Allyson-Robert/SpaceTimeGlobe/Images/001-A.png

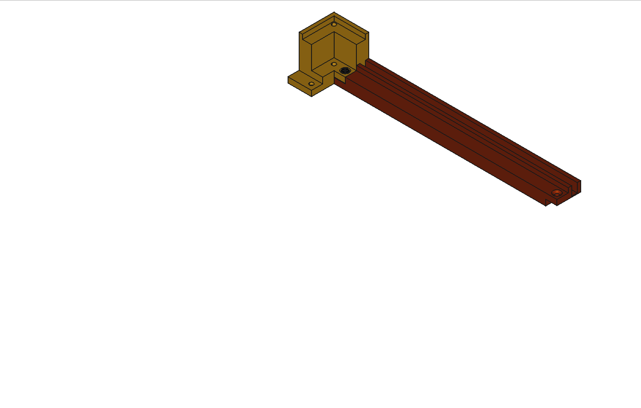
Images/001-A.png
