Allyson-Robert/SpaceTimeGlobe/Images/001.png

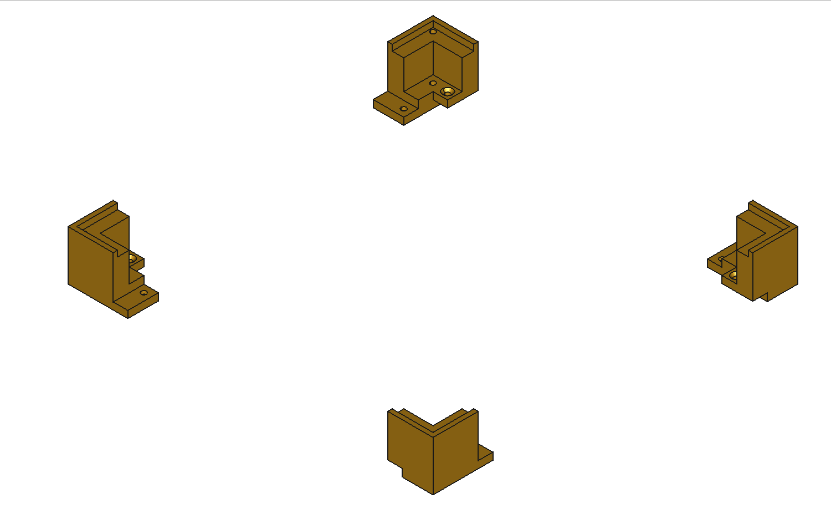
Images/001.png
