Allyson-Robert/SpaceTimeGlobe/Images/002.png

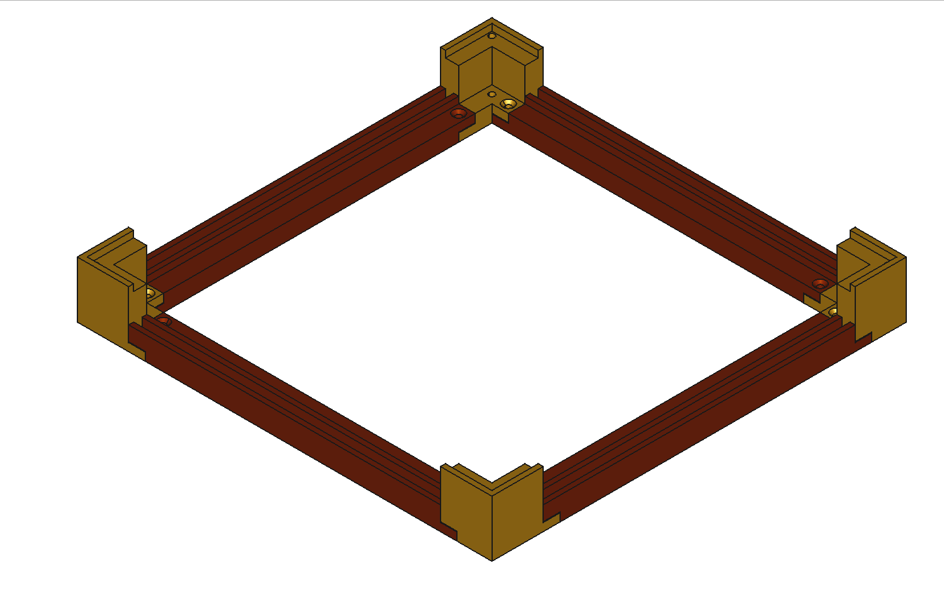
Images/002.png
