Allyson-Robert/SpaceTimeGlobe/Images/004.png

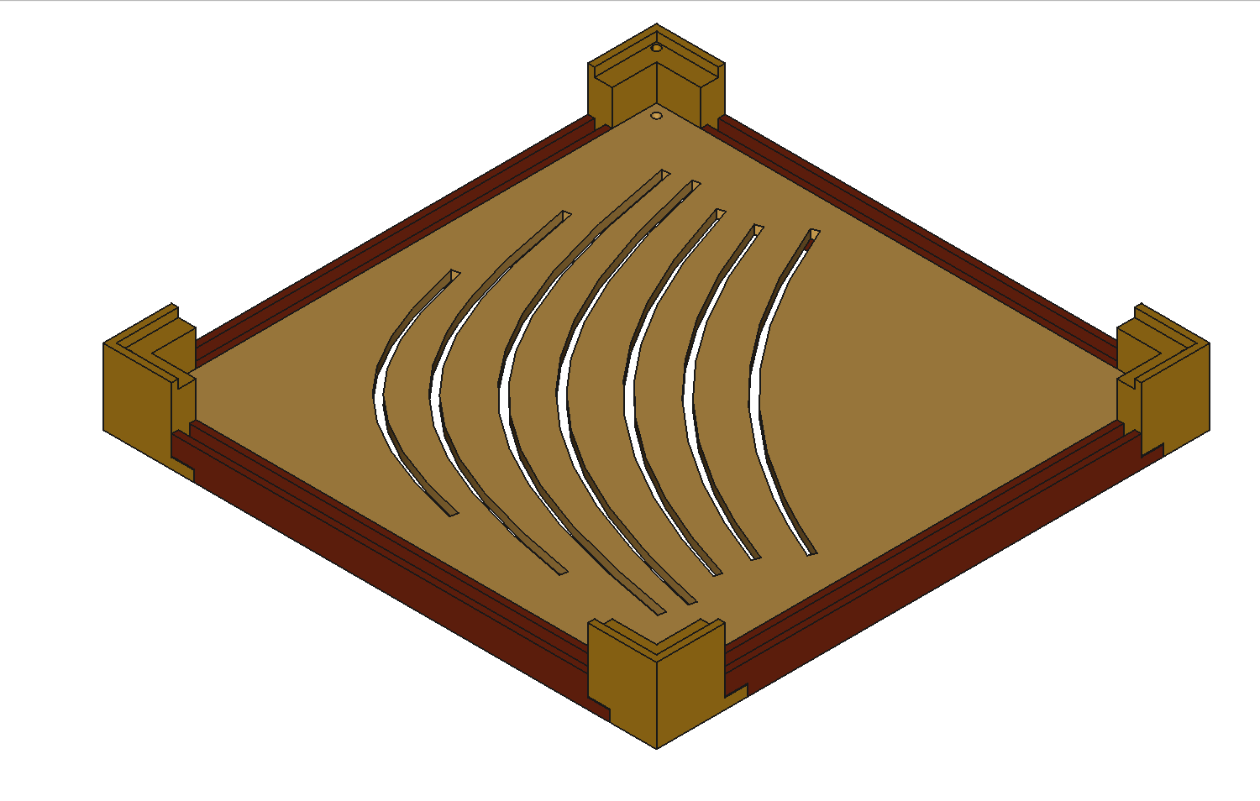
Images/004.png
