Allyson-Robert/SpaceTimeGlobe/Images/007.png

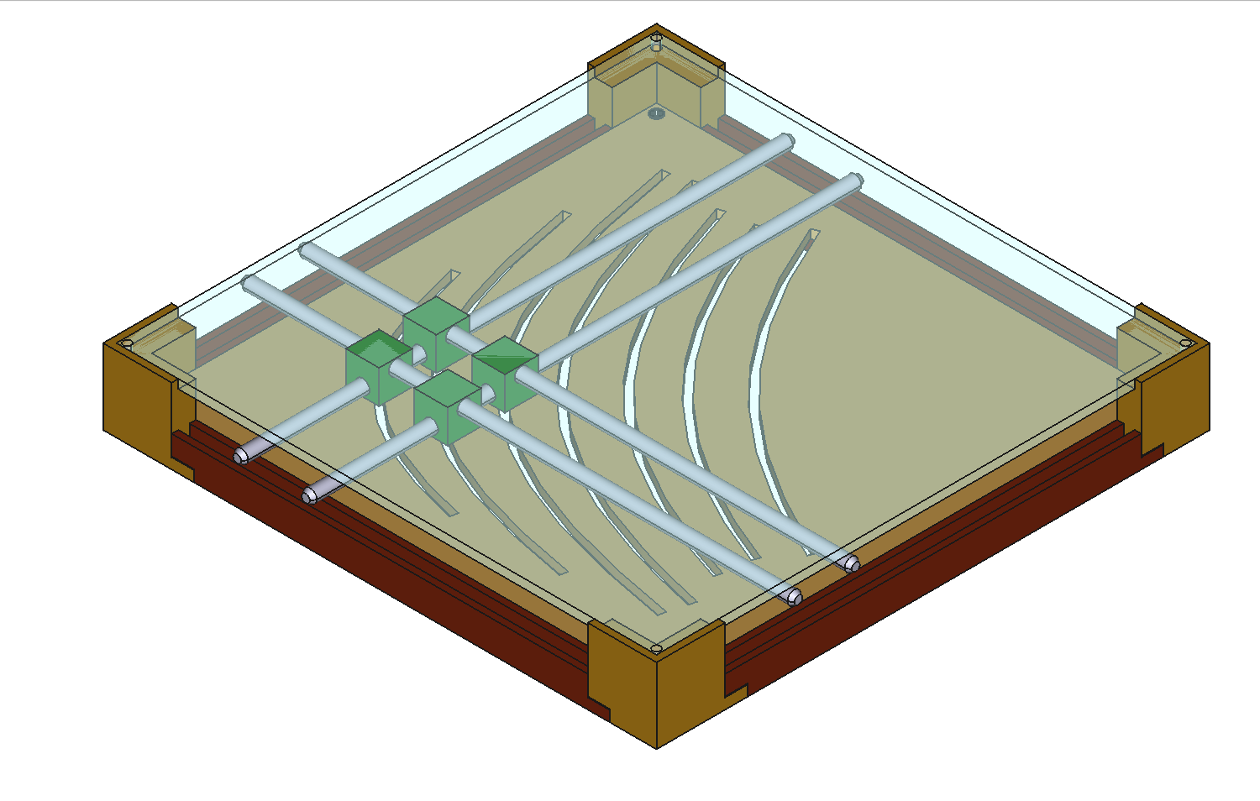
Images/007.png
